ryan-tenerowicz/qmk_firmware/keyboards/rtenerowicz/rev2/cad/trackpoint top 1.stl

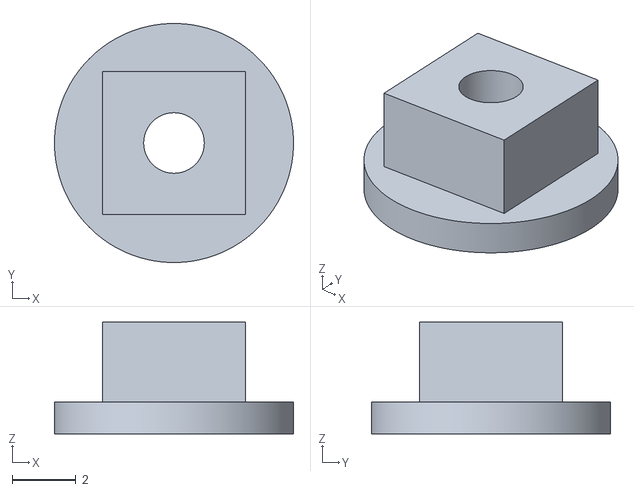
[picture p19: CAD file, 2024-06-19]
keyboards/rtenerowicz/rev2/cad/trackpoint top 1.stl
7.50 x 7.50 x 3.50
