ryan-tenerowicz/qmk_firmware/keyboards/rtenerowicz/rev2/cad/mouse buttons.stl

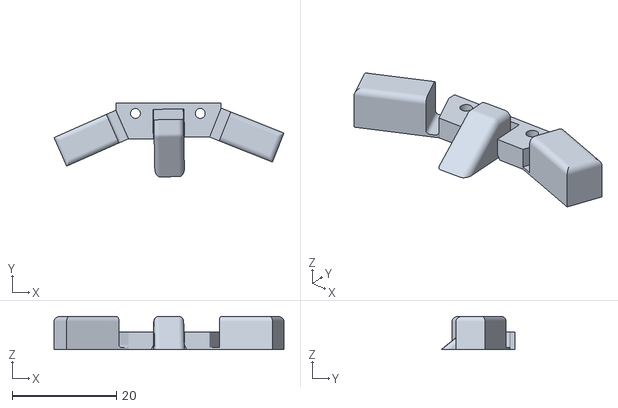
[picture p20: CAD file, 2024-06-19]
keyboards/rtenerowicz/rev2/cad/mouse buttons.stl
44.2 x 14.2 x 6.40
