ryan-tenerowicz/qmk_firmware/keyboards/rtenerowicz/rev2/cad/angle block.3mf

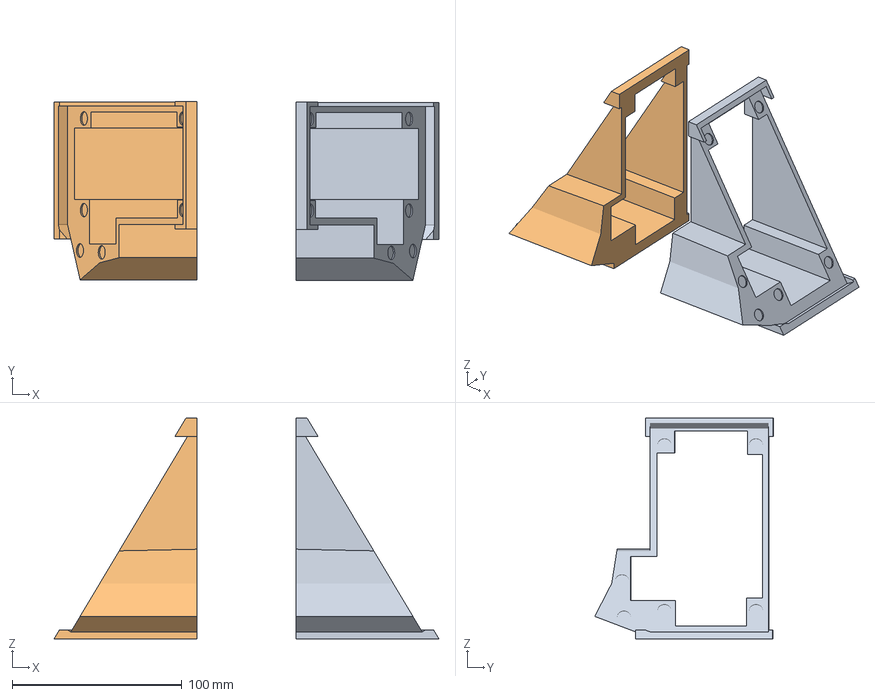
[picture p21: CAD file, 2024-06-19]
keyboards/rtenerowicz/rev2/cad/angle block.3mf
227.0 x 105.3 x 130.3 mm
angle block.stl x 2
