ryan-tenerowicz/qmk_firmware/keyboards/rtenerowicz/rev2/cad/trackpoint bottom.stl

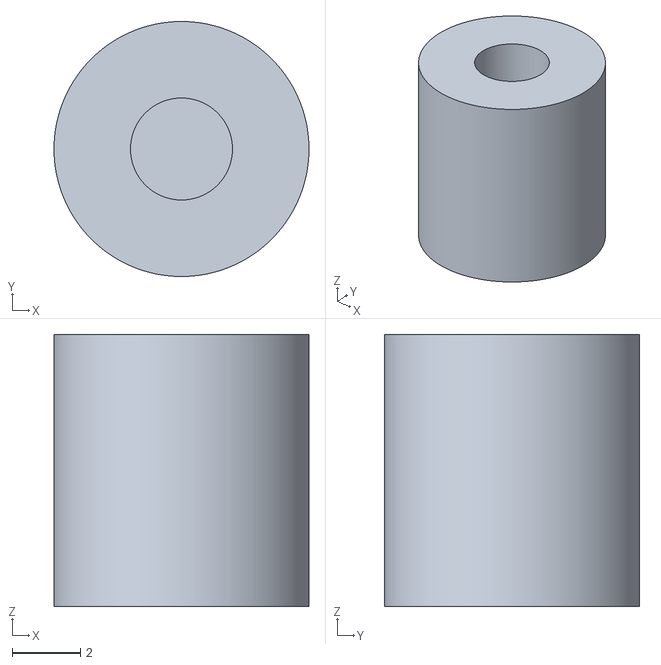
[picture p22: CAD file, 2024-06-19]
keyboards/rtenerowicz/rev2/cad/trackpoint bottom.stl
7.50 x 7.50 x 8.00
