ryan-tenerowicz/qmk_firmware/keyboards/rtenerowicz/rev2/cad/trackpoint stick.stl

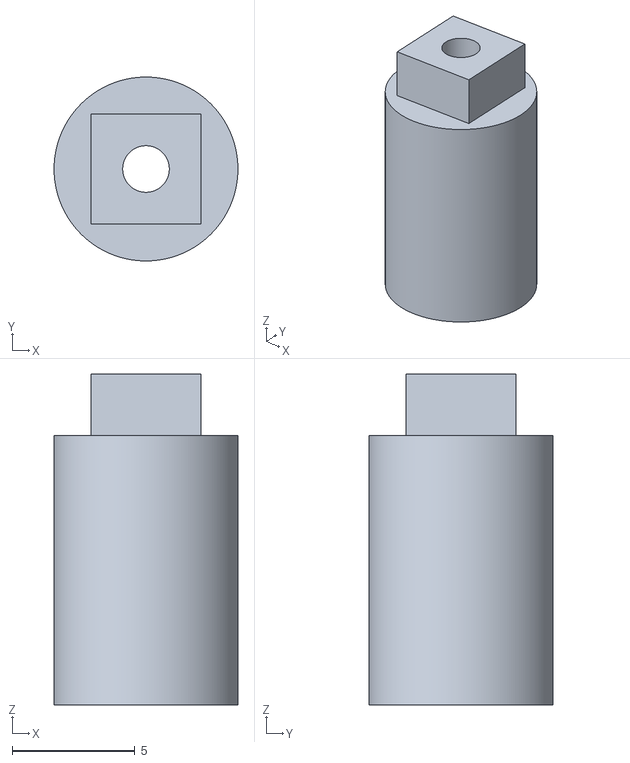
[picture p23: CAD file, 2024-06-19]
keyboards/rtenerowicz/rev2/cad/trackpoint stick.stl
7.50 x 7.50 x 13.5
