ryan-tenerowicz/qmk_firmware/keyboards/rtenerowicz/rev2/cad/mouse buttons 6.3mf

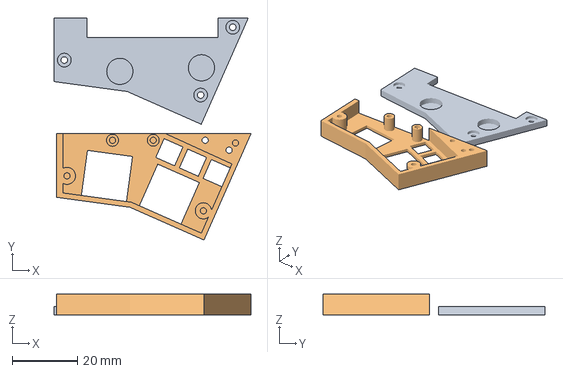
[picture p24: CAD file, 2024-06-19]
keyboards/rtenerowicz/rev2/cad/mouse buttons 6.3mf
60.2 x 67.8 x 6.30 mm
thumb together bottom.stl
thumb together top.stl
