ryan-tenerowicz/qmk_firmware/keyboards/rtenerowicz/rev2/cad/thumb together top.3mf

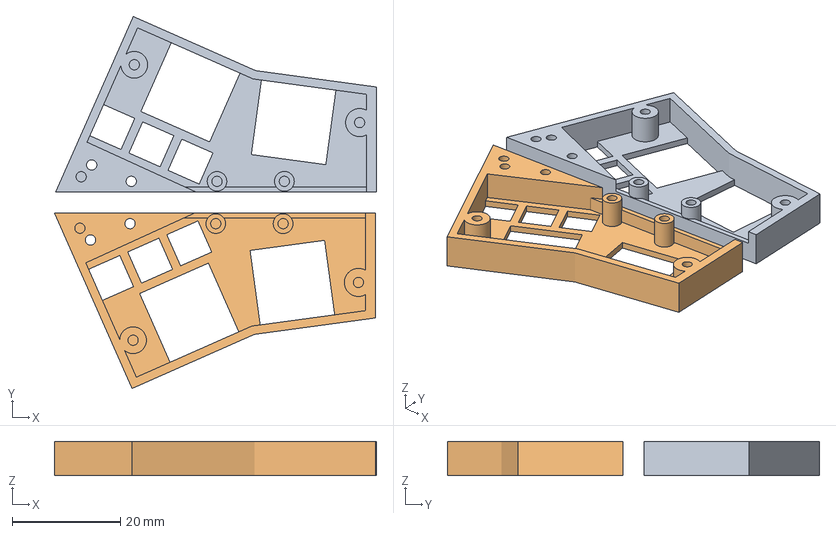
[picture p25: CAD file, 2024-06-19]
keyboards/rtenerowicz/rev2/cad/thumb together top.3mf
59.6 x 68.8 x 6.30 mm
thumb together top.stl x 2
