ryan-tenerowicz/qmk_firmware/keyboards/rtenerowicz/rev2/cad/trackpoint top 5.stl

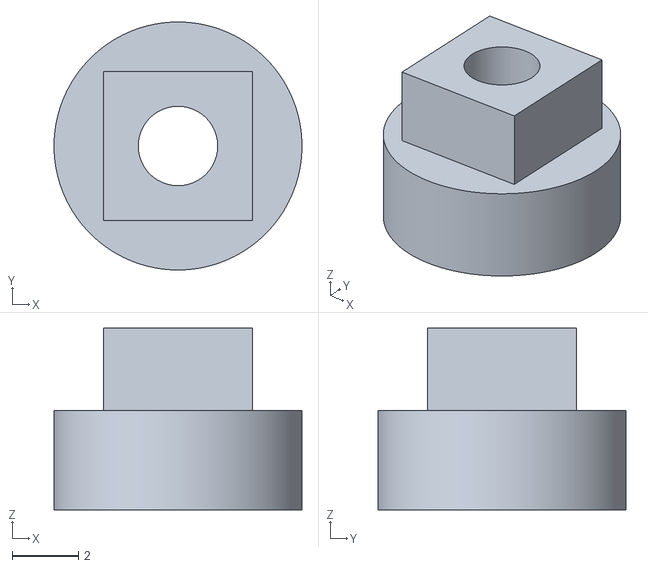
[picture p26: CAD file, 2024-06-19]
keyboards/rtenerowicz/rev2/cad/trackpoint top 5.stl
7.50 x 7.50 x 5.50
