ryan-tenerowicz/qmk_firmware/keyboards/rtenerowicz/rev2/cad/case.stl

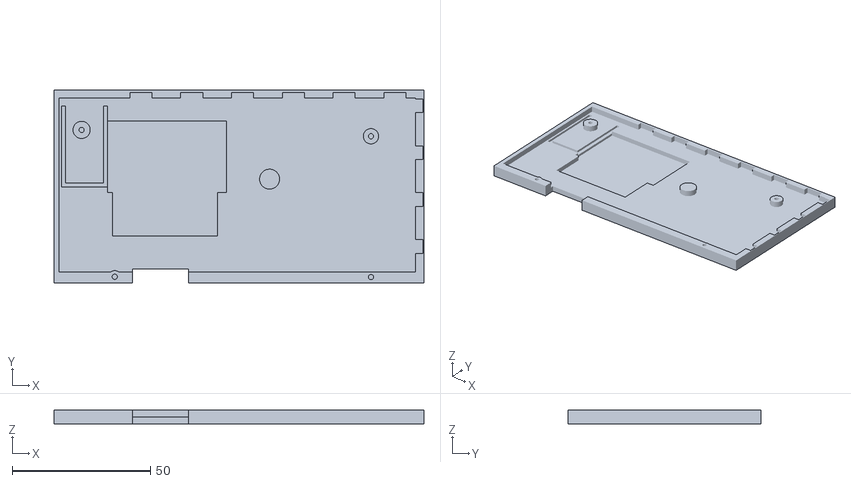
[picture p27: CAD file, 2024-06-19]
keyboards/rtenerowicz/rev2/cad/case.stl
134.0 x 70.0 x 5.00
