ryan-tenerowicz/qmk_firmware/keyboards/rtenerowicz/rev2/cad/thumb_bottom.stl

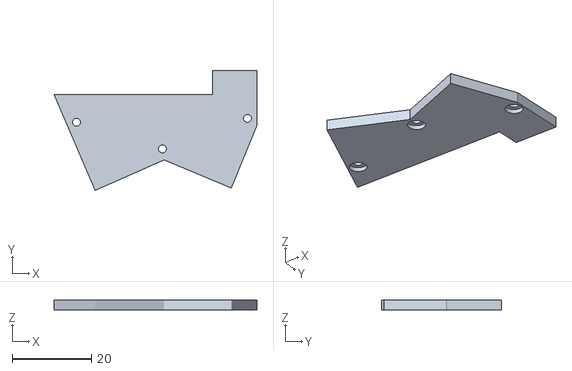
[picture p28: CAD file, 2024-06-19]
keyboards/rtenerowicz/rev2/cad/thumb_bottom.stl
51.2 x 30.2 x 2.50
