ryan-tenerowicz/qmk_firmware/keyboards/rtenerowicz/rev2/cad/thumb.stl

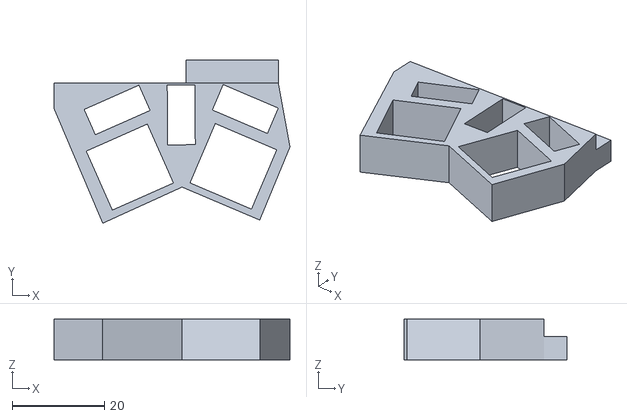
[picture p29: CAD file, 2024-06-19]
keyboards/rtenerowicz/rev2/cad/thumb.stl
51.2 x 35.5 x 8.80
