ryan-tenerowicz/qmk_firmware/keyboards/rtenerowicz/lynxware/config.h

#define TAPPING_TERM 175

#define ANALOG_JOYSTICK_X_AXIS_PIN F7
#define ANALOG_JOYSTICK_Y_AXIS_PIN F6
#define ANALOG_JOYSTICK_SPEED_MAX 5
#define ANALOG_JOYSTICK_WEIGHTS {0,2,4,5,7,8,9,10,12,13,14,15,15,16,17,18,18,19,19,20,20,21,21,21,22,22,22,22,23,23,23,23,23,23,23,23,23,23,23,23,23,23,23,23,23,23,23,23,23,23,24,24,24,24,24,24,25,25,25,26,26,26,27,28,28,29,29,30,31,32,33,34,35,36,37,38,40,41,43,44,46,48,49,51,53,56,58,60,62,65,68,70,73,76,79,82,85,89,92,96,100}


//#define MATRIX_COL_PINS_RIGHT { E6, B4, B5, B7, C7, F1, F0, B6, B2 }
//#define MATRIX_ROW_PINS_RIGHT { D3, D4, C6, D7, B3, B1 }
#define DIODE_DIRECTION ROW2COL

#define SPLIT_HAND_PIN B0
#define USE_I2C
#define SPLIT_MAX_CONNECTION_ERRORS 10
#define SPLIT_CONNECTION_CHECK_TIMEOUT 10
